barrettotte/vacuum-tube-toolbox/examples/plugin_coil.scad

include <../VacuumTubes/coils.scad>

// openscad -o examples/plugin_coil.stl examples/plugin_coil.scad

$fs = 0.1;
$fn = 60;

tolerance = 0.1;

plugin_coil_mounted(height=70, wall_thickness=2.5, bottom_thickness=3.5, pins=4, 
    core_diameter=31.75, pin_diameter=2.20-0.10, wire_hole_diameter=1.75+tolerance,
    mount_hole_diameter=3, mount_width=15);
