barrettotte/vacuum-tube-toolbox/examples/single_tube_holder.scad

include <../VacuumTubes/holders.scad>

$fs = 0.1;
$fn = 60;

tube_holder(rows=1, cols=1, socket_diameter=27.75, socket_tolerance=0.1, 
    socket_padding=5, socket_depth=7, height=10, edge_padding=2.5);
